danjulio/iCam/firmware/pictures/icam_fw_arch.jpg

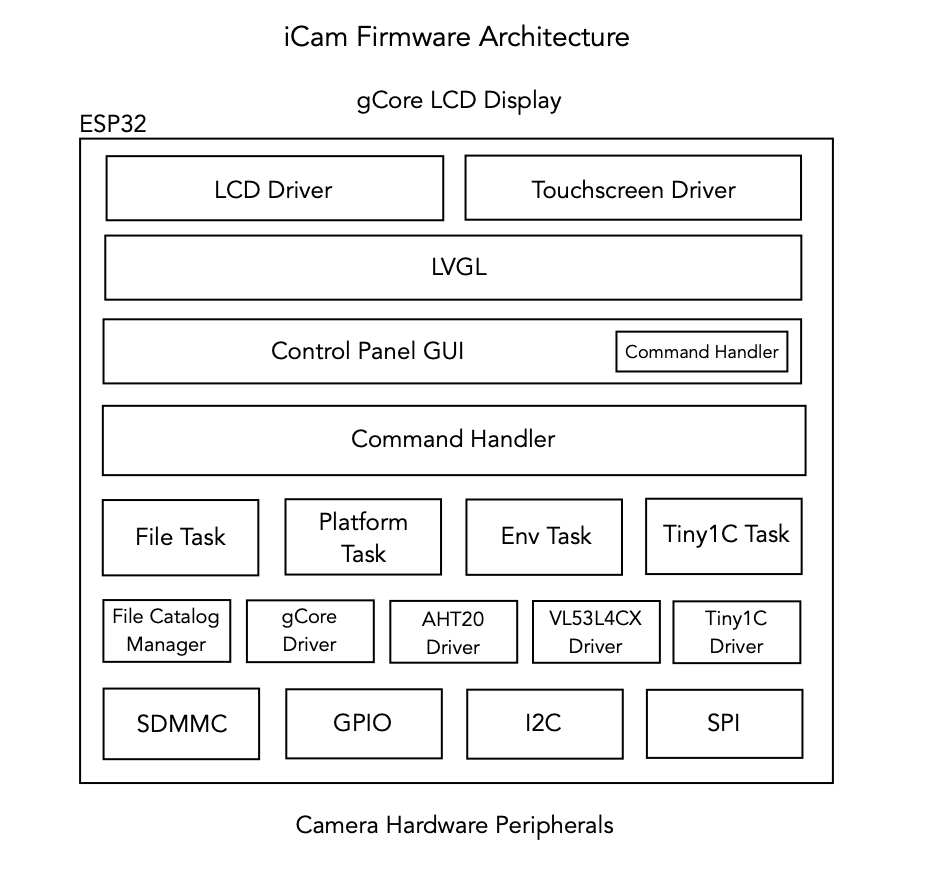
firmware/pictures/icam_fw_arch.jpg
