danjulio/iCam/firmware/pictures/icam_mini_vid_fw_arch.jpg

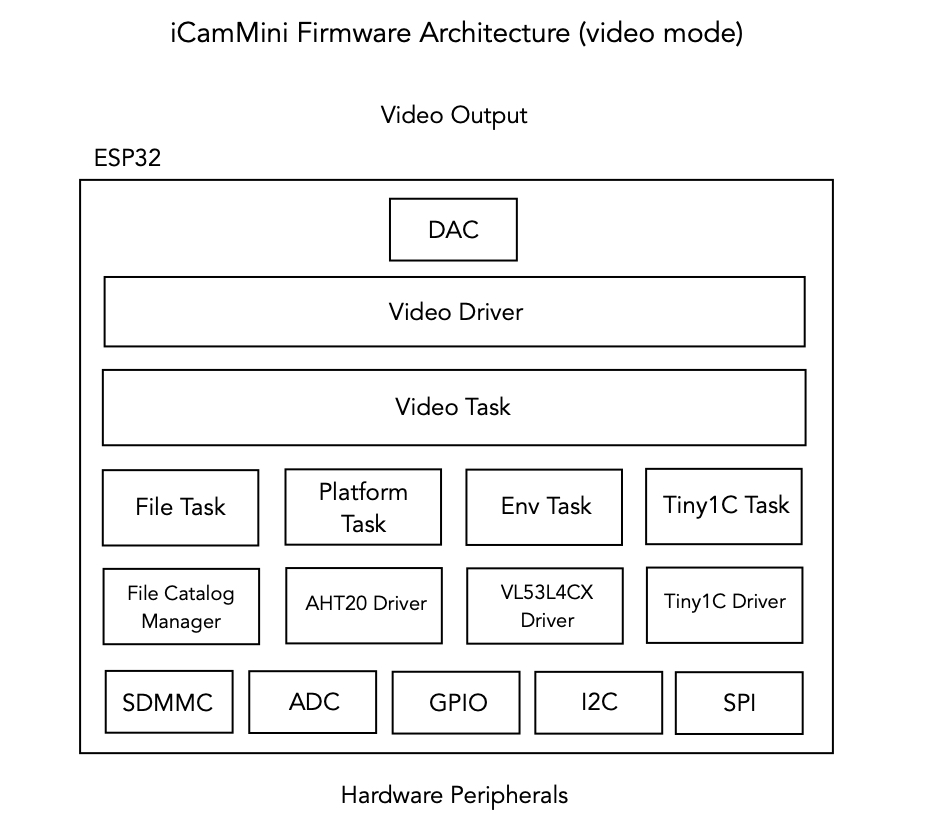
firmware/pictures/icam_mini_vid_fw_arch.jpg
