danjulio/iCam/iCamMini/pictures/iCamMini_block_diagram.jpg

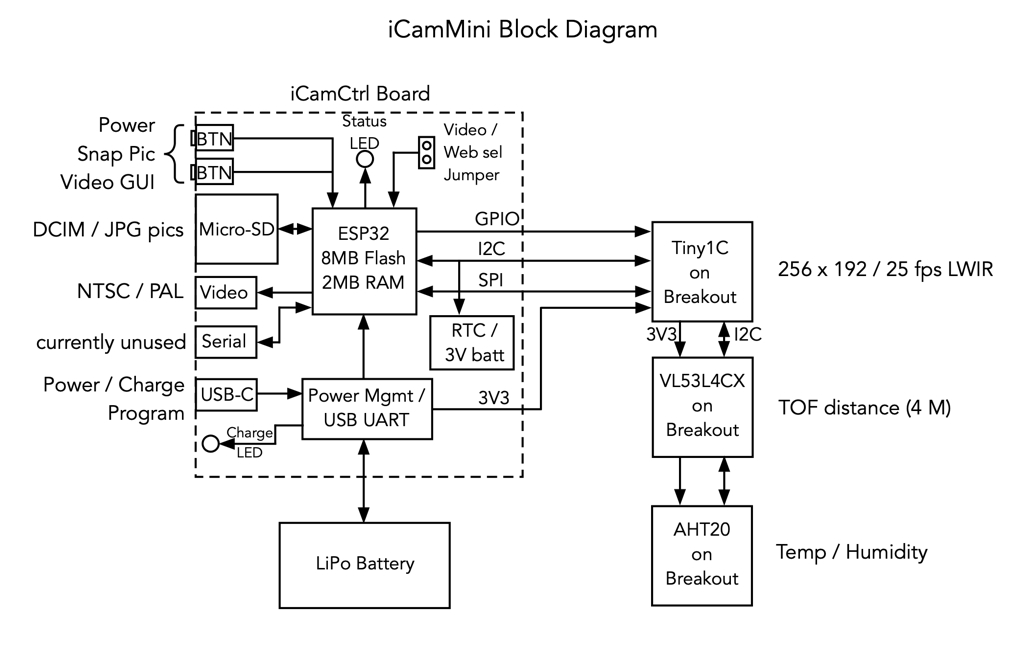
iCamMini/pictures/iCamMini_block_diagram.jpg
