danjulio/iCam/Tiny1C_breakout/pictures/Tiny1C_breakout_rev3_pcb_top.png

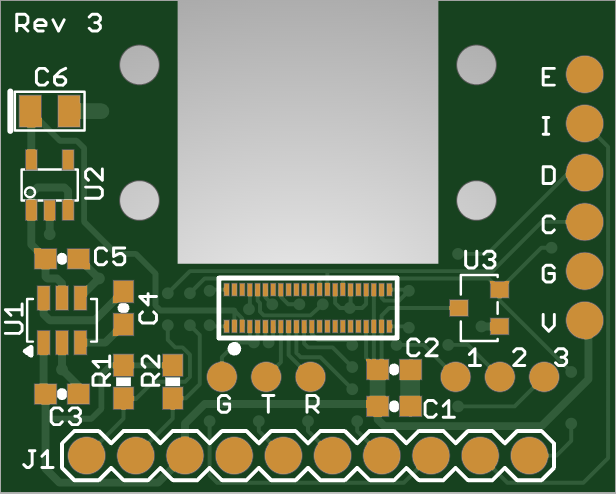
Tiny1C_breakout/pictures/Tiny1C_breakout_rev3_pcb_top.png
